tguyenn/vrbomb/firmware/inc/Arabic.c

// Arabic.h
// Runs on MSPM0
// Arabic output to ST7735R
// Amina Meddad and Jonathan Valvano
// 8/21/2024

#include "../inc/Arabic.h"
#include "../inc/ST7735.h"

// n wide by 16 tall 16-bit images
// width n is encoded in array name/number
const uint16_t alif4[] = {
 0xFFFF, 0xFFFF, 0xFFFF, 0xFFFF, 0xFFFF, 0xFFFF, 0xFFFF, 0xFFFF, 0xFFFF, 0xFFFF, 0xFFFF, 0xFFFF, 0xFFFF, 0xFFFF, 0xFFFF, 0xFFFF,
 0xFFFF, 0x0000, 0xFFFF, 0xFFFF, 0xFFFF, 0x0000, 0x0000, 0xFFFF, 0xFFFF, 0x0000, 0x0000, 0xFFFF, 0xFFFF, 0x0000, 0x0000, 0xFFFF,
 0xFFFF, 0x0000, 0x0000, 0xFFFF, 0xFFFF, 0x0000, 0x0000, 0xFFFF, 0xFFFF, 0x0000, 0x0000, 0xFFFF, 0xFFFF, 0x0000, 0x0000, 0xFFFF,
 0xFFFF, 0x0000, 0x0000, 0xFFFF, 0xFFFF, 0x0000, 0x0000, 0xFFFF, 0xFFFF, 0x3186, 0x0000, 0xFFFF, 0xFFFF, 0xFFFF, 0x0000, 0xFFFF
};
const uint16_t ayh11[] = {
 0xFFFF, 0xFFFF, 0xFFFF, 0x0000, 0x0000, 0x0000, 0x0000, 0x0000, 0xF7BE, 0xFFFF, 0xFFFF, 0xFFFF, 0xFFFF, 0x0000, 0x0000, 0x0861,
 0x6B6D, 0x73AE, 0x4208, 0x0000, 0x0000, 0xFFFF, 0xFFFF, 0xE71C, 0x0000, 0xFFFF, 0xFFFF, 0xFFFF, 0xFFFF, 0xFFFF, 0xFFFF, 0xFFFF,
 0xFFFF, 0xFFFF, 0x0841, 0xFFFF, 0xFFFF, 0xFFFF, 0xFFFF, 0xFFFF, 0xFFFF, 0xFFFF, 0xFFFF, 0xFFFF, 0xFFFF, 0x5AEB, 0xFFFF, 0xFFFF,
 0xFFFF, 0xFFFF, 0xFFFF, 0xFFFF, 0xFFFF, 0xFFFF, 0xFFFF, 0xFFFF, 0xFFFF, 0x2104, 0xFFFF, 0xFFFF, 0xFFFF, 0xFFFF, 0xFFFF, 0xFFFF,
 0xFFFF, 0xFFFF, 0xFFFF, 0xFFFF, 0x0000, 0xFFFF, 0xFFFF, 0xFFFF, 0xFFFF, 0xFFFF, 0xFFFF, 0xFFFF, 0xFFFF, 0xFFFF, 0xFFFF, 0xFFFF,
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
 0xFFFF, 0xFFFF, 0xFFFF, 0xFFFF, 0xFFFF, 0xFFFF, 0xFFFF, 0xFFFF, 0xFFFF, 0xFFFF, 0xFFFF, 0xFFFF, 0xFFFF, 0xFFFF, 0xFFFF, 0xFFFF,
 0xFFFF, 0xFFFF, 0xFFFF, 0xFFFF, 0xFFFF, 0xFFFF, 0xFFFF, 0xFFFF, 0xFFFF, 0xFFFF, 0xFFFF, 0xFFFF, 0xFFFF, 0xFFFF, 0xFFFF, 0xFFFF
};



const uint16_t *ArabicFont[]= {0,alif4,ayh11,baa13 ,daad16,daal8 ,dhaa14 ,dhaal8  ,faa16  ,ghayh11 ,haa8  ,ha11,jeem12  ,kaaf12  ,khaa12  ,laam12  ,meem9  ,noon12  ,qaaf12  ,raa9  ,saad16  ,seen16  ,sheen16  ,ta14 ,thaa14 ,twe14  ,waaw11  ,yaa14  ,zaa9, space8, dot8 };
const uint32_t ArabicWidth[]= {0,4,11,13,16,8 ,14 ,8  ,16  ,11 ,8  ,11,12  ,12  ,12  ,12  ,9  ,12  ,12  ,9  ,16  ,16  ,16  ,14 ,14 ,14    ,11  ,14  ,9, 8, 8 };

uint32_t ArabicX,ArabicY; // cursor
//********Arabic_SetCursor*****************
// Move the cursor to the desired X- and Y-position.  The
// next character will be printed here.  X=0 is the leftmost
// column.  Y=0 is the top row.
// inputs: newX  new X-position of the cursor (0<=newX<=127)
//         newY  new Y-position of the cursor (0<=newY<=159)
// outputs: none
void Arabic_SetCursor(uint32_t newX, uint32_t newY){
  if((newX > 127) || (newY > 159)){    // bad input
    return;                            // do nothing
  }
  ArabicX = newX;
  ArabicY = newY;
}
// *************** Arabic_OutChar ********************
// Output one character to the LCD
// Position determined by Arabic_SetCursor command
// Inputs: 8-bit Arabic character
// Outputs: none
void Arabic_OutChar(Arabic_t ch){
    uint32_t w = ArabicWidth[ch];
  if((ArabicX+w)>127){ // won't fit
    ArabicX = 0;
    ArabicY += 16;
    if(ArabicY>159){
      ArabicY = 15;
    }
  }
  ST7735_DrawBitmap(ArabicX,ArabicY,ArabicFont[ch],w,16);
  ArabicX += w;
}
//********Arabic_OutString*****************
// Print a string of Arabic characters to the ST7735 LCD.
// Position determined by Arabic_SetCursor command
// The string will automatically wrap.
// inputs: ptr  pointer to end-terminated Arabic string
// outputs: none
void Arabic_OutString(Arabic_t *ptr){
  while(*ptr != null){
    Arabic_OutChar(*ptr);
    ptr = ptr + 1;
  }
}
