tguyenn/vrbomb/firmware/inc/Key.c

/* Key.c
 * Students put your names here
 * Modified: January 12, 2026
 * 4-bit keyboard connected to PB19-PB16
 * Piano key 3 PB19 (note with highest frequency)
 * Piano key 2 PB18
 * Piano key 1 PB17
 * Piano key 0 PB16 (note with lowest frequency)
 *
 */
#include <ti/devices/msp/msp.h>
#define PB16INDEX 32 // UART2_RX  SPI1_SCK  UART3_RTS TIMG8_C1  TIMG7_C1
#define PB17INDEX 42 // UART2_TX  SPI0_PICO SPI1_CS1  TIMA1_C0  TIMA0_C2
#define PB18INDEX 43 // UART2_RX  SPI0_SCK  SPI1_CS2  TIMA1_C1  TIMA0_C2N
#define PB19INDEX 44 // COMP2_OUT SPI0_POCI TIMG8_C1  UART0_CTS TIMG7_C1
#include "../inc/LaunchPad.h"

// **************Key_Init*********************
// Initialize piano key inputs on PB19-PB16
// Input: none
// Output: none
void Key_Init(void){
// Assumes LaunchPad_Init has been called
// I.e., PortB has already been reset and activated (do not reset PortB here again)
    // regular inputs

}

// **************Key_In*********************
// Input from piano key inputs on PB19-PB16
// Input: none
// Output: 0 to 15 depending on keys
//   0x01 is just Key0, 0x02 is just Key1, 0x04 is just Key2, 0x08 is just Key3
uint32_t Key_In(void){
    // regular Lab5

 return 42; // replace this line
 

}
